Rahul-2-specs/Wearable-Foot-Motion-Energy-Harvester/simulation/Step_counter.asc

C1: cap; 1µC
R1: res; 100KR
R2: res; 1MegR
U1: UniversalOpAmp2
V1: voltage; SINE(0 0.5 2)
V2: voltage; 0.1
V3: voltage; 5V
V4: voltage; 5V
Named nets: 0
.tran 10 startup
