Rahul-2-specs/Wearable-Foot-Motion-Energy-Harvester/simulation/db107.asc

C1: cap; 10µC
C2: cap; 2200µc
D1: diode; DDB107
D2: diode; DDB107
D3: diode; DDB107
D4: diode; DDB107
R1: res; 220KR
R2: res; 1MegR
V1: voltage; SINE(0 4 2)
Named nets: 0
.model DDB107 D(Is=2n Rs=0.3 N=1.9 Cjo=15p Bv=1000 Ibv=5u)
.tran 1000 startup
