Rahul-2-specs/Wearable-Foot-Motion-Energy-Harvester/simulation/Full_wave_rect.asc

C1: cap; 1000µC
R1: res; 100KR
U1: TBAT54
U2: TBAT54
U3: TBAT54
U4: TBAT54
V1: voltage; SINE(0 1.2 2)
Named nets: 0
.tran 200
