Rahul-2-specs/Wearable-Foot-Motion-Energy-Harvester/simulation/Half_wave_rect.asc

C1: cap; 1µC
C2: cap; 100µC
R1: res; 220KR
R2: res; 1MegR
U1: TBAT54
U2: TBAT54
V1: voltage; SINE(0 4 2)
Named nets: 0
.tran 250 startup
