Rahul-2-specs/Wearable-Foot-Motion-Energy-Harvester/simulation/LTC3588(1).asc

C2: cap; 100µ; V=6.3V
I1: current; PULSE(0 30m 5 1u 1u 10m 3)
L1: ind; 22µ; Ipk=0.75 Rser=0.19
Rload: res; 500K
U1: LTC3588-1
V1: voltage; SINE(0 7 100); Rser=10K
V2: voltage; 5
Named nets: OUT, 0
.tran 0 5 startup
LTC3588-1,  Piezoelectric Energy Harvesting Power Supply with Simulated Remote Sensor/Transmitter
Input: 24V 41Hz  Rs=119K     Output: 3.3V with 30mA 10msec Pulse Load
Piezoelectric Device
MIDE V22BL
1.4 Gpk Force at 41Hz
with Tip Mass of 1 gm.
