Rahul-2-specs/Wearable-Foot-Motion-Energy-Harvester/simulation/piezo_teng_harvester.asc

C1: cap; 47nC
C2: cap; 100µC
D1: diode
D2: diode
D3: diode
D4: diode
D5: LED
I1: current; SINE(0 20uA 100)
R1: res; 100kR
Named nets: 0
.tran 0.5s
