Rahul-2-specs/Wearable-Foot-Motion-Energy-Harvester/simulation/switching_circuit.asc

C1: cap; 470µC
C2: cap; 0.1µC
M1: pmos; IRLML6402
M2: pmos; IRLML6402
M3: pmos
R1: res; 1MegR
R2: res; 1MegR
R3: res; 8kR
R4: res; 20kR
R5: res; 100kR
V_BAT: voltage; 2.4
V_HARV: voltage; PWL(0 0  1 0.5  2 1  3 2  4 3  6 3  7 2  8 1  9 0)
Named nets: 0
.tran 10
